AndreasFMueller/Focuser/software/fclient.c

/*
 * fclient.c -- client program for the focuser
 *
 * (c) 2016 Prof Dr Andreas Mueller, Hochschule Rapperswil
 */
#include <stdlib.h>
#include <stdio.h>
#include <libusb-1.0/libusb.h>
#include <unistd.h>
#include <getopt.h>
#include <string.h>

/*
 * we have to find out whether this is a sufficiently modern libusb.
 * unfortunately, older libusb implementations have no way to tell 
 * what version they are. But maybe the presence of the LIBUSB_ERROR_COUNT
 * preprocessor symbol allows us to recognize sufficiently modern 
 * libusb for a full implementation
 */

#ifndef LIBUSB_ERROR_COUNT
#define LIBUSB_LOG_LEVEL_INFO	3
#define LIBUSB_LOG_LEVEL_DEBUG	4
char	*libusb_strerror(int rc) {
	switch (rc) {
	case  0:
		return "Success";
	case -1:
		return "IO error";
	case -2:
		return "invalid parameter";
	case -3:
		return "access denied";
	case -4:
		return "no device";
	case -5:
		return "not found";
	case -6:
		return "busy";
	case -7:
		return "timeout";
	case -8:
		return "overflow";
	case -9:
		return "pipe error";
	case -10:
		return "system call interrupted";
	case -11:
		return "insufficient memory";
	case -12:
		return "not supported";
	}
	return "other error";
}
#endif /* LIBUSB_ERROR_COUNT */

/*
 * commands understood by the Focuser device
 */
#define FOCUSER_RESET	0
#define FOCUSER_GET	1
#define FOCUSER_SET	2
#define FOCUSER_LOCK	3
#define FOCUSER_RCVR	4
#define FOCUSER_STOP	5
#define FOCUSER_SAVED	6
#define FOCUSER_SERIAL	7
#define FOCUSER_POSITION	8
#define FOCUSER_TOPSPEED	9

/*
 * display the descriptors, for tesing
 */
int	show_descriptors(libusb_device_handle *handle) {
	libusb_device	*device = libusb_get_device(handle);

	// get the descriptors
	struct libusb_device_descriptor	device_descriptor;
	libusb_get_device_descriptor(device, &device_descriptor);
	printf("bLength:            %d\n", device_descriptor.bLength);
	printf("bDescriptorType:    %d\n", device_descriptor.bDescriptorType);
	printf("bcdUSB:             %x\n", device_descriptor.bcdUSB);
	printf("bDeviceClass:       %x\n", device_descriptor.bDeviceClass);
	printf("bDeviceSubClass:    %x\n", device_descriptor.bDeviceSubClass);
	printf("bDeviceProtocol:    %x\n", device_descriptor.bDeviceProtocol);
	printf("bMaxPacketSize0:    %d\n", device_descriptor.bMaxPacketSize0);
	printf("idVendor:           0x%04x\n", device_descriptor.idVendor);
	printf("idProduct:          0x%04x\n", device_descriptor.idProduct);
	unsigned char	s[128];
	if (device_descriptor.iManufacturer) {
		int	rc = libusb_get_string_descriptor_ascii(handle,
			device_descriptor.iManufacturer, s, sizeof(s));
		if (rc < 0) {
			snprintf((char *)s, sizeof(s), "error: %s (%d)",
				libusb_error_name(rc), rc);
		}
		printf("Manufacturer:       %s\n", s);
	}
	if (device_descriptor.iProduct) {
		int	rc = libusb_get_string_descriptor_ascii(handle,
			device_descriptor.iProduct, s, sizeof(s));
		if (rc < 0) {
			snprintf((char *)s, sizeof(s), "error: %s (%d)",
				libusb_error_name(rc), rc);
		}
		printf("Product:            %s\n", s);
	}
	if (device_descriptor.iSerialNumber) {
		int	rc = libusb_get_string_descriptor_ascii(handle,
			device_descriptor.iSerialNumber, s, sizeof(s));
		if (rc < 0) {
			snprintf((char *)s, sizeof(s), "error: %s (%d)",
				libusb_error_name(rc), rc);
		}
		printf("Serial Number:      %s\n", s);
	}
	printf("bNumConfigurations: %d\n", device_descriptor.bNumConfigurations);

	struct libusb_config_descriptor	*config_descriptor;
	if (libusb_get_config_descriptor(device, 0, &config_descriptor)) {
		fprintf(stderr, "cannot get config descriptor\n");
		return EXIT_FAILURE;
	}
	printf("    bLength:              %d\n",
		config_descriptor->bLength);
	printf("    bDescriptorType:      %d\n",
		config_descriptor->bDescriptorType);
	printf("    wTotalLength:         %d\n",
		config_descriptor->wTotalLength);
	printf("    bNumInterfaces:       %d\n",
		config_descriptor->bNumInterfaces);
	printf("    bConfigurationValue:  %d\n",
		config_descriptor->bConfigurationValue);
	if (config_descriptor->iConfiguration) {
		int	rc = libusb_get_string_descriptor_ascii(handle,
				config_descriptor->iConfiguration, s, sizeof(s));
		if (rc < 0) {
			snprintf((char *)s, sizeof(s), "error: %s (%d)",
				libusb_error_name(rc), rc);
		}
		printf("iConfiguration:     %s\n", s);
	}
	printf("    bmAttributes:         %d\n",
		config_descriptor->bmAttributes);
	printf("    MaxPower:             %d\n",
		2 * config_descriptor->MaxPower);
	return EXIT_SUCCESS;
}

extern void	show_version();

/*
 * Show usage message
 */
void	usage(const char *progname) {
	printf("Client program to control the othello Focuser controller hardware.\n");
	printf("Usage:\n\n");
	printf("  %s [ options ] get\n", progname);
	printf("  %s [ options ] set <value>\n", progname);
	printf("  %s [ options ] up\n", progname);
	printf("  %s [ options ] down\n", progname);
	printf("  %s [ options ] stop\n", progname);
	printf("  %s [ options ] position <value>\n\n", progname);
	printf("To move the focuser to a new position, use the set command. Fast moves can\n");
	printf("be done using the -f option. Stop movement with the stop command, and stay\n");
	printf("informed about the current position of the moving focuser using the get\n");
	printf("command. The up and down commands are equivalent to setting the extreme\n");
	printf("values of the focuser. The position command sets the internal focuser\n");
	printf("position without moving the motor.\n\n");
	printf("  %s [ options ] receiver\n", progname);
	printf("  %s [ options ] [ lock | unlock ]\n\n", progname),
	printf("Get information about the receiver buttons, lock or unlock the them\n\n");
	printf("  %s [ options ] reset\n", progname);
	printf("  %s [ options ] descriptors\n", progname);
	printf("  %s [ options ] serial <serial>\n", progname);
	printf("  %s [ options ] gettop\n", progname);
	printf("  %s [ options ] settop <0-3>\n", progname);
	printf("  %s [ options ] help\n\n", progname);
	printf("The reset command reboots the focuser hardware. The descriptors command\n");
	printf("displays the USB descriptors of the device, shows serial number among others.\n");
	printf("The help command displays this message, just like the --help option.\n\n");
	printf("Options:\n");
	printf("  -d,--debug           enable USB debugging\n");
	printf("  -f,--fast            fast movement (500 steps/s instead of 62, \n");
	printf("                       set command only\n");
	printf("  -h,-?,--help         display this help and exit\n");
	printf("  -p,--product=<pid>   use this product id to connect (default 0x1235)\n");
	printf("  -v,--vendor=<vid>    use this vendor id to connect (default 0xf055)\n");
	printf("  -V,--version         show version of USB library and exit\n");
}


static struct option	longopts[] = {
{ "debug",		no_argument,		NULL,	'd' },
{ "fast",		no_argument,		NULL,	'f' },
{ "help",		no_argument,		NULL,	'h' },
{ "vendor",		required_argument,	NULL,	'v' },
{ "product",		required_argument,	NULL,	'p' },
{ "version",		no_argument,		NULL,	'V' },
{ NULL,			0,			NULL,	 0  }
};

/*
 * Main function of the client program
 */
int	main(int argc, char *argv[]) {
	// parse command line
	int	c;
	int	debug = 0;
	uint16_t	vid = 0xf055;
	uint16_t	pid = 0x1235;
	int	fast = 0;
	int	longindex;
	while (EOF != (c = getopt_long(argc, argv, "dfh?v:p:V",
			longopts, &longindex)))
		switch (c) {	
		case 'd':
			debug = 1;
			break;
		case 'f':
			fast = 1;
			break;
		case 'h':
		case '?':
			usage(argv[0]);
			return EXIT_SUCCESS;
		case 'v':
			vid = atoi(optarg);
			break;
		case 'p':
			pid = atoi(optarg);
			break;
		case 'V':
			show_version();
			return EXIT_SUCCESS;
		}

	// get the command
	if (optind >= argc) {
		fprintf(stderr, "command argument missing\n");
		return EXIT_FAILURE;
	}
	char	*command = argv[optind++];

	// handle the help command, just for completeness
	if (0 == strcmp(command, "help")) {
		usage(argv[0]);
		return EXIT_SUCCESS;
	}
	

	// initialize libusb library
	libusb_context	*context;
	libusb_init(&context);
	libusb_set_debug(context,
		(debug) ? LIBUSB_LOG_LEVEL_DEBUG : LIBUSB_LOG_LEVEL_INFO);

	// connect to the device
	libusb_device_handle *handle;
	handle = libusb_open_device_with_vid_pid(context, vid, pid);
	if (NULL == handle) {
		fprintf(stderr, "cannot open device\n");
		return EXIT_FAILURE;
	}

	// process the descriptors command
	if (0 == strcmp(command, "descriptors")) {
		return show_descriptors(handle);
	}

	// commands below may need to evaluate the USB return code
	int		rc;

	// the command interpreter for commands using the same USB commands
	// usually starts off with the command set to an invalid command,
	// and only does something, if the command is set
	uint8_t		cmd = 0xff;

	// all commands need value and index, so we allocate these variables
	// only once
	uint16_t	value = 0;
	uint16_t	index = 0;
	int32_t		position = 0;

	// set command implementation
	index = (fast) ? 1 : 0;
	if (0 == strcmp(command, "set")) {
		if (optind >= argc) {
			fprintf(stderr, "no argument to set given\n");
			return EXIT_SUCCESS;
		}
		position = atoi(argv[optind++]);
		cmd = FOCUSER_SET;
	}
	if (0 == strcmp(command, "up")) {
		position = 0xfffffe;
		cmd = FOCUSER_SET;
	}
	if (0 == strcmp(command, "down")) {
		position = 0x000001;
		cmd = FOCUSER_SET;
	}
	if (cmd == FOCUSER_SET) {
		fprintf(stderr, "target position: %d\n", position);
		rc = libusb_control_transfer(handle,
			LIBUSB_REQUEST_TYPE_VENDOR |
			LIBUSB_RECIPIENT_DEVICE |
			LIBUSB_ENDPOINT_OUT, cmd, 
			value, index, (unsigned char *)&position,
			sizeof(position), 1000);
		if (rc < 0) {
			fprintf(stderr, "cannot send SET: %s\n", 
				libusb_strerror(rc));
			return EXIT_FAILURE;
		}
		return EXIT_SUCCESS;
	}

	// get command implementation
	if (0 == strcmp(command, "get")) {
		index = 0xf;
		int32_t	result[3];
		rc = libusb_control_transfer(handle,
			LIBUSB_REQUEST_TYPE_VENDOR |
			LIBUSB_RECIPIENT_DEVICE |
			LIBUSB_ENDPOINT_IN, FOCUSER_GET, 
			0, index, (unsigned char *)result, sizeof(result), 1000);
		if (rc < 0) {
			fprintf(stderr, "cannot send GET: %s\n", 
				libusb_strerror(rc));
			return EXIT_FAILURE;
		}
		if (rc != sizeof(result)) {
			fprintf(stderr, "focuser position not received\n");
			return EXIT_FAILURE;
		}
		if (result[0] == result[1]) {
			printf("current: %d, target: %d\n",
				result[0], result[1]);
		} else {
			printf("current: %d, target: %d, speed: %s\n",
				result[0], result[1],
				(result[2]) ? "fast" : "slow");
		}
		return EXIT_SUCCESS;
	}

	// get the configured top speed
	if (0 == strcmp(command, "gettop")) {
		unsigned char	result;
		rc = libusb_control_transfer(handle,
			LIBUSB_REQUEST_TYPE_VENDOR |
			LIBUSB_RECIPIENT_DEVICE |
			LIBUSB_ENDPOINT_IN, FOCUSER_TOPSPEED, 
			0, 0, (unsigned char *)&result, sizeof(result), 1000);
		if (rc < 0) {
			fprintf(stderr, "cannot send TOPSPEED command: %s\n",
				libusb_strerror(rc));
			return EXIT_FAILURE;
		}
		if (rc != 1) {
			fprintf(stderr, "focuser top speed not received\n");
			return EXIT_FAILURE;
		}
		printf("top speed: %d\n", (int)result);
		return EXIT_SUCCESS;
	}

	// set command implementation
	if (0 == strcmp(command, "saved")) {
		int32_t	result;
		rc = libusb_control_transfer(handle,
			LIBUSB_REQUEST_TYPE_VENDOR |
			LIBUSB_RECIPIENT_DEVICE |
			LIBUSB_ENDPOINT_IN, FOCUSER_SAVED, 
			0, 0, (unsigned char *)&result, sizeof(result), 1000);
		if (rc < 0) {
			fprintf(stderr, "cannot send GET: %s\n", 
				libusb_strerror(rc));
			return EXIT_FAILURE;
		}
		if (rc != sizeof(result)) {
			fprintf(stderr, "focuser position not received\n");
			return EXIT_FAILURE;
		}
		printf("saved: %d\n", result);
		return EXIT_SUCCESS;
	}

	// stop command implementation
	if (0 == strcmp(command, "stop")) {
		rc = libusb_control_transfer(handle,
			LIBUSB_REQUEST_TYPE_VENDOR |
			LIBUSB_RECIPIENT_DEVICE |
			LIBUSB_ENDPOINT_OUT, FOCUSER_STOP, 
			0, 0, NULL, 0, 1000);
		if (rc < 0) {
			fprintf(stderr, "cannot send STOP: %s\n", 
				libusb_strerror(rc));
			return EXIT_FAILURE;
		}
		return EXIT_SUCCESS;
	}

	// receiver command implementation
	if (0 == strcmp(command, "receiver")) {
		unsigned char	result;
		rc = libusb_control_transfer(handle,
			LIBUSB_REQUEST_TYPE_VENDOR |
			LIBUSB_RECIPIENT_DEVICE |
			LIBUSB_ENDPOINT_IN, FOCUSER_RCVR, 
			0, 0, (unsigned char *)&result, 1, 1000);
		if (rc < 0) {
			fprintf(stderr, "cannot send RCVR: %s\n", 
				libusb_strerror(rc));
			return EXIT_FAILURE;
		}
		if (rc != 1) {
			fprintf(stderr, "button status not received\n");
			return EXIT_FAILURE;
		}
		printf("receiver status: %c%c%c%c%s\n",
			(result & 0x01) ? 'A' : '_',
			(result & 0x02) ? 'B' : '_',
			(result & 0x04) ? 'C' : '_',
			(result & 0x08) ? 'D' : '_',
			(result & 0x80) ? " (locked)" : ""
		);
		return EXIT_SUCCESS;
	}

	// lock/unlock command
	cmd = 0xff;
	if (0 == strcmp(command, "lock")) {
		index = 1;
		cmd = FOCUSER_LOCK;
	}
	if (0 == strcmp(command, "unlock")) {
		index = 0;
		cmd = FOCUSER_LOCK;
	}
	if (cmd == FOCUSER_LOCK) {
		rc = libusb_control_transfer(handle,
			LIBUSB_REQUEST_TYPE_VENDOR |
			LIBUSB_RECIPIENT_DEVICE |
			LIBUSB_ENDPOINT_OUT, FOCUSER_LOCK, 
			0, index, NULL, 0, 1000);
		if (rc) {
			fprintf(stderr, "cannot send LOCK: %s\n", 
				libusb_strerror(rc));
			return EXIT_FAILURE;
		}
		return EXIT_SUCCESS;
	}

	// serial command
	if (0 == strcmp(command, "serial")) {
		if (optind >= argc) {
			fprintf(stderr, "serial number string missing\n");
			return EXIT_FAILURE;
		}
		char	*newserial = argv[optind];
		int	l = strlen(newserial);
		if (l > 7) {
			fprintf(stderr, "serial string '%s' too long (%d > 7)\n",
				newserial, l);
			return EXIT_FAILURE;
		}
		rc = libusb_control_transfer(handle,
			LIBUSB_REQUEST_TYPE_VENDOR |
			LIBUSB_RECIPIENT_DEVICE |
			LIBUSB_ENDPOINT_OUT, FOCUSER_SERIAL, 
			0, 0, (unsigned char *)newserial, l, 1000);
		if (rc < 0) {
			fprintf(stderr, "cannot send SERIAL '%s': %s\n", 
				newserial, libusb_strerror(rc));
			return EXIT_FAILURE;
		}
		if (rc != l) {
			fprintf(stderr, "cannot send %d bytes: %d\n", l, rc);
			return EXIT_FAILURE;
		}
		return EXIT_SUCCESS;
	}

	// reset command
	if (0 == strcmp(command, "reset")) {
		rc = libusb_control_transfer(handle,
			LIBUSB_REQUEST_TYPE_VENDOR |
			LIBUSB_RECIPIENT_DEVICE |
			LIBUSB_ENDPOINT_OUT, FOCUSER_RESET, 
			0, 0, NULL, 0, 1000);
		if (rc) {
			fprintf(stderr, "cannot send RESET: %s (%d)\n", 
				libusb_strerror(rc), rc);
			return EXIT_FAILURE;
		}
		return EXIT_SUCCESS;
	}

	// position command
	if (0 == strcmp(command, "position")) {
		if (optind >= argc) {
			fprintf(stderr, "position argument missing\n");
			return EXIT_FAILURE;
		}
		uint32_t	position = atoi(argv[optind]);
		rc = libusb_control_transfer(handle,
			LIBUSB_REQUEST_TYPE_VENDOR |
			LIBUSB_RECIPIENT_DEVICE |
			LIBUSB_ENDPOINT_OUT, FOCUSER_POSITION, 
			value, index, (unsigned char *)&position,
			sizeof(position), 1000);
		if (rc < 0) {
			fprintf(stderr, "cannot send POSITION: %s\n", 
				libusb_strerror(rc));
			return EXIT_FAILURE;
		}
		if (rc != sizeof(position)) {
			fprintf(stderr, "could not send position %u\n",
				position);
			return EXIT_FAILURE;
		}
		return EXIT_SUCCESS;
	}

	// set topspeed command
	if (0 == strcmp(command, "settop")) {
		if (optind >= argc) {
			fprintf(stderr, "top speed argument missing\n");
			return EXIT_FAILURE;
		}
		unsigned char	topspeed = atoi(argv[optind]);
		if (topspeed > 3) {
			fprintf(stderr, "not a valid top speed value\n");
			return EXIT_FAILURE;
		}
		rc = libusb_control_transfer(handle,
			LIBUSB_REQUEST_TYPE_VENDOR |
			LIBUSB_RECIPIENT_DEVICE |
			LIBUSB_ENDPOINT_OUT, FOCUSER_TOPSPEED, 
			0, 0, (unsigned char *)&topspeed,
			sizeof(topspeed), 1000);
		if (rc < 0) {
			fprintf(stderr, "cannot send TOPSPEED: %s\n", 
				libusb_strerror(rc));
			return EXIT_FAILURE;
		}
		if (rc != sizeof(topspeed)) {
			fprintf(stderr, "could not send position %u\n",
				(int)topspeed);
			return EXIT_FAILURE;
		}
		return EXIT_SUCCESS;
	}

	// command was not interpreted
	fprintf(stderr, "unknown command '%s'\n", command);
	return EXIT_FAILURE;
}
