AndreasFMueller/Focuser/firmware/timer.h

/*
 * timer.h -- timer definitions
 *
 * (c) 2016 Prof Dr Andreas Mueller, Hochschule Rapperswil
 */
#ifndef _timer_h
#define _timer_h

extern uint8_t	resetflag;

extern void 	timer_stop();
extern void	timer_start();

#endif /* _timer_h */
