AndreasFMueller/Focuser/firmware/led.h

/*
 * led.h -- control interface to the LED
 *
 * (c) 2016 Prof Dr Andreas Mueller, Hochschule Rapperswil
 */
#ifndef _led_h
#define _led_h

void	led_on();
void	led_off();
void	led_value(unsigned char v);

#endif /* _led_h */
